crithvikbhaskar/Battery-managemnet-system/bms_pcb/bms_pcb.kicad_sch

## KiCad design bms_pcb/bms_pcb.kicad_sch (2025-11-05)

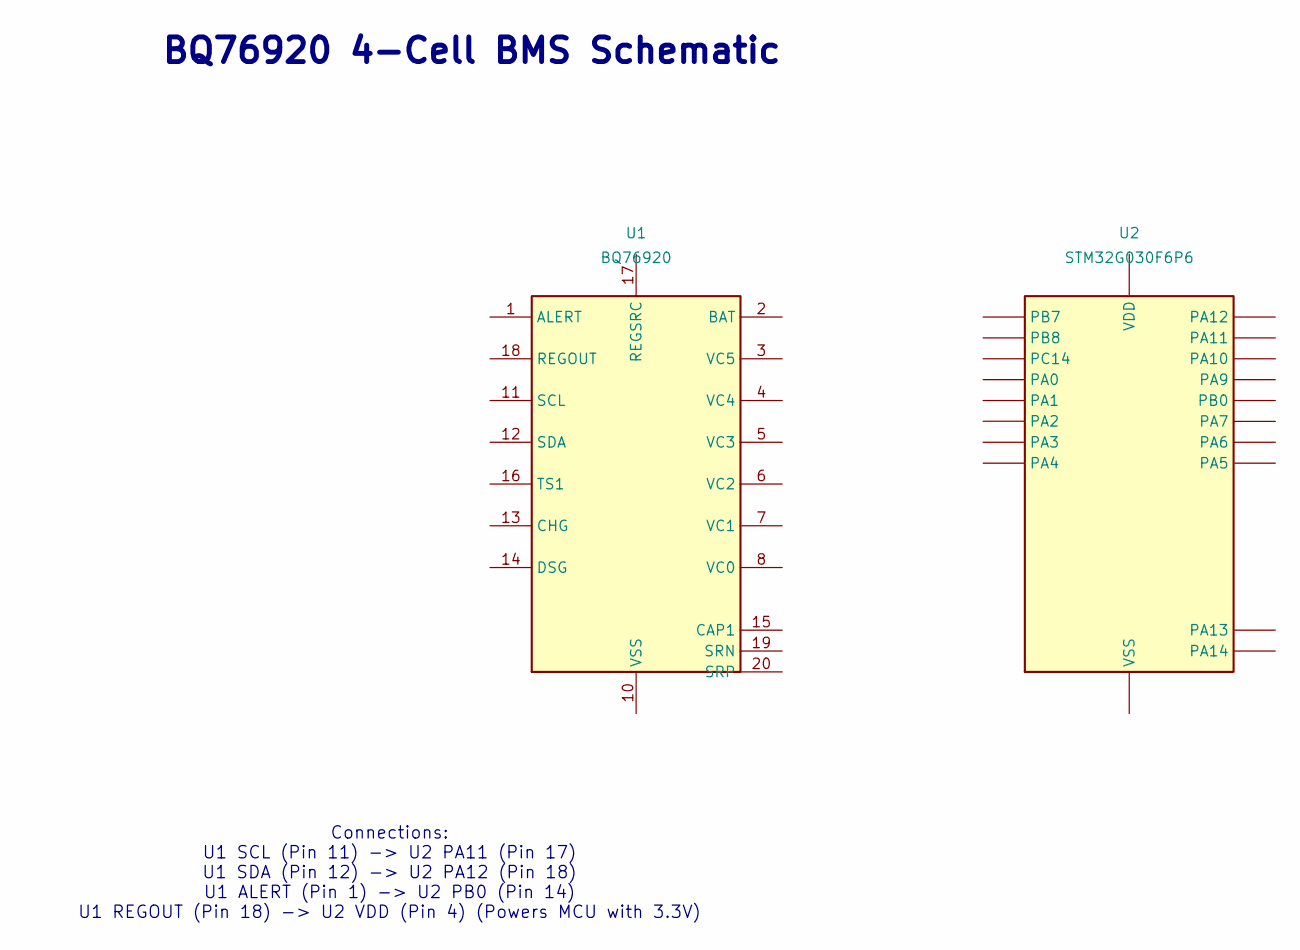
[picture p3: schematic bms_pcb.kicad_sch]

Parts:
U1: BQ76920; TSSOP-20_4.4x6.5mm_P0.65mm
U2: STM32G030F6P6; TSSOP-20_4.4x6.5mm_P0.65mm

Notes on the sheet:
BQ76920 4-Cell BMS Schematic
Connections: U1 SCL (Pin 11) -> U2 PA11 (Pin 17) U1 SDA (Pin 12) -> U2 PA12 (Pin 18) U1 ALERT (Pin 1) -> U2 PB0 (Pin 14) U1 REGOUT (Pin 18) -> U2 VDD (Pin 4) (Powers MCU with 3.3V)
